Lougous/sunps2/board/sunps2.kicad_sch

## KiCad design board/sunps2.kicad_sch (2023-11-17)

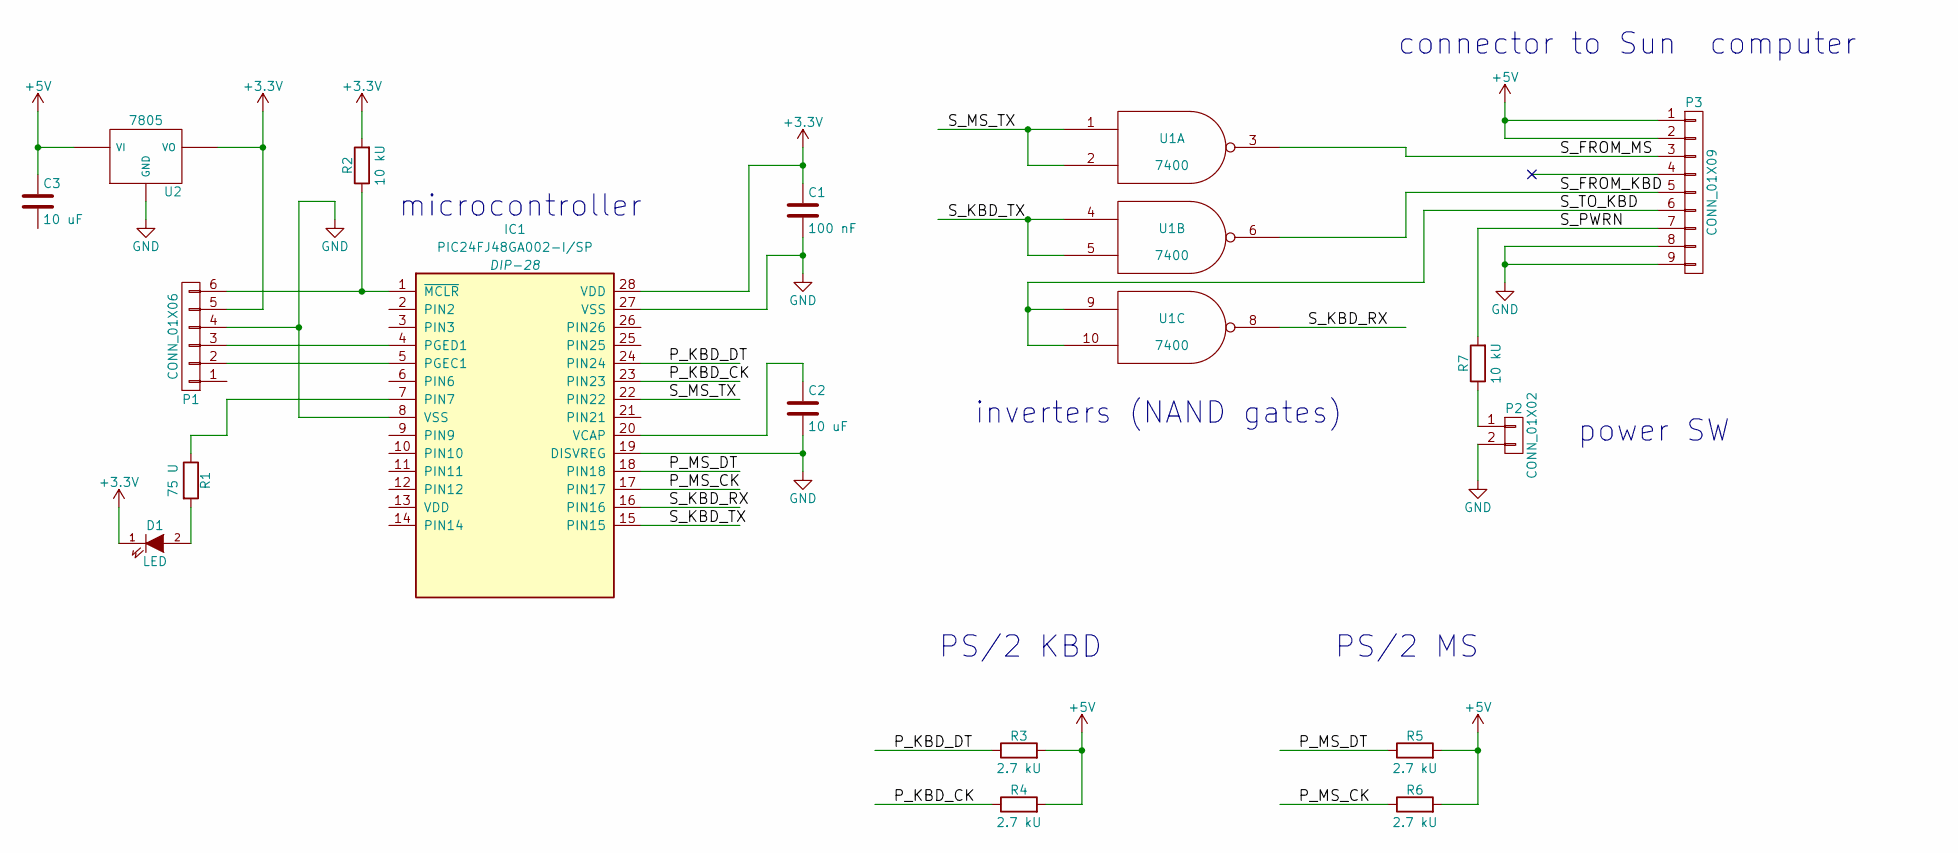
[picture p2: schematic sunps2.kicad_sch]

Parts:
C1: 100 nF; C_Disc_D6_P5
C2: 10 uF; C_Disc_D6_P5
C3: 10 uF
D1: LED; LED-3MM
IC1: PIC24FJ48GA002-I/SP; DIP-28
P1: CONN_01X06; PINHEAD1-6
P2: CONN_01X02
P3: CONN_01X09
R1: 75 U; Resistor_Horizontal_RM7mm
R2, R7: 10 kU; Resistor_Horizontal_RM7mm
R3, R4, R5, R6: 2.7 kU; Resistor_Horizontal_RM7mm
U1: 7400; DIP-14_W7.62mm
U2: 7805

Connections:
+3.3V: C1.1, D1.1 (K), IC1.28 (VDD), P1.5, R2.2, U2.VO
+5V: C3.1, P3.1, P3.2, R3.2, R4.2, R5.2, R6.2, U2.VI
GND: C1.2, C2.2, IC1.8 (VSS), IC1.19 (DISVREG), IC1.27 (VSS), P1.4, P2.2, P3.8, P3.9, U2.GND
unnamed: C2.1, IC1.20 (VCAP)
unnamed: D1.2 (A), R1.2
unnamed: IC1.1 (~MCLR), P1.6, R2.1
unnamed: IC1.4 (PGED1), P1.3
unnamed: IC1.5 (PGEC1), P1.2
unnamed: IC1.7 (PIN7), R1.1
unnamed: P2.1, R7.1
P_KBD_CK: IC1.23 (PIN23), R4.1
P_KBD_DT: IC1.24 (PIN24), R3.1
P_MS_CK: IC1.17 (PIN17), R6.1
P_MS_DT: IC1.18 (PIN18), R5.1
S_FROM_KBD: P3.5, U1.6
S_FROM_MS: P3.3, U1.3
S_KBD_RX: IC1.16 (PIN16), U1.8
S_KBD_TX: IC1.15 (PIN15), U1.4, U1.5
S_MS_TX: IC1.22 (PIN22), U1.1, U1.2
S_PWRN: P3.7, R7.2
S_TO_KBD: P3.6, U1.9, U1.10

Notes on the sheet:
PS/2 KBD
PS/2 MS
connector to Sun computer
inverters (NAND gates)
power SW
microcontroller
