Lougous/sunps2/soft/keymap.h

const unsigned char ps2_to_sun_tbl[128] = {
	0x0 , //  0 (0) : 
	0x12, //  1 (1) : F9
	0x0 , //  2 (2) : 
	0x0C, //  3 (3) : F5
	0x08, //  4 (4) : F3
	0x05, //  5 (5) : F1
	0x06, //  6 (6) : F2
	0x01, //  7 (7) : F12 => STOP (F12=0x0B)
	0x0 , //  8 (8) : 
	0x07, //  9 (9) : F10
	0x11, //  A (10): F8
	0x0E, //  B (11): F6
	0x0A, //  C (12): F4
	0x35, //  D (13): TAB
	0x2A, //  E (14): `  (FR: ^2)
	0x0 , //  F (15): 
	0x0 , // 10 (16): 
	0x13, // 11 (17): LALT
	0x6E, // 12 (18): LSHIFT
	0x0 , // 13 (19): 
	0x4C, // 14 (20): LCTRL
	0x36, // 15 (21): Q
	0x1E, // 16 (22): 1
	0x0 , // 17 (23): 
	0x0 , // 18 (24): 
	0x0 , // 19 (25): 
	0x64, // 1A (26): Z
	0x4E, // 1B (27): S
	0x4D, // 1C (28): A
	0x37, // 1D (29): W
	0x1F, // 1E (30): 2
	0x0 , // 1F (31): 
	0x0 , // 20 (): 
	0x66, // 21 (): C
	0x65, // 22 (): X
	0x4F, // 23 (): D
	0x38, // 24 (): E
	0x21, // 25 (): 4
	0x20, // 26 (): 3
	0x0 , // 27 (): 
	0x0 , // 28 (): 
	0x79, // 29 (): SPACE
	0x67, // 2A (): V
	0x50, // 2B (): F
	0x3A, // 2C (): T
	0x39, // 2D (): R
	0x22, // 2E (): 5
	0x0 , // 2F (): 
	0x0 , // 30 () : 
	0x69, // 31 (1) : N
	0x68, // 32 (2) : B
	0x52, // 33 (3) : H
	0x51, // 34 (4) : G
	0x3B, // 35 (5) : Y
	0x23, // 36 (6) : 6
	0x0 , // 37 (7) : 
	0x0 , // 38 (8) : 
	0x0 , // 39 (9) : 
	0x6A, // 3A (10):    (FR: ,)
	0x53, // 3B (11): J
	0x3C, // 3C (12): U
	0x24, // 3D (13): 7
	0x25, // 3E (14): 8
	0x0 , // 3F (15): 
	0x0 , // 40 (0) : 
	0x6B, // 41 (1) : ,  (FR: ;)
	0x54, // 42 (2) : K
	0x3D, // 43 (3) : I
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
	0x14, //  75 : up arrow
	0x0 , //  76 : 
	0x0 , //  77 :
	0x0 , //  78 : 
	0x0 , //  79 : 
	0x7B, //  7A : page down
	0x0 , //  7B : 
	0x0 , //  7C : 
	0x60, //  7D : page up
	0x0 , //  7E : 
	0x0 , //  7F : 
};

// 0x0E, 83 : F7

// https://kentie.net/article/sunkbd/page2.htm
